MinghaoCheng/Pacman/host/src/Drivers/ldr_matrix.h

/*
 * GNU GENERAL PUBLIC LICENSE
 * Version 1, Mar 2019
 *
 * (C) 2019, Minghao Cheng <chengminghao92@gmail.com>
 */
#ifndef _LDR_MATRIX_
#define _LDR_MATRIX_

#include <stdint.h>

#include "./../BSP/mcp23s17.h"
#include "./../util/Thread.h"
#include "./../util/callback.h"
#include "brd_config.h"

/**
 * Class of Light-Dependent-Resistor matrix
 */
class LDR_matrix: public callback
{
    public:
    LDR_matrix(pthread_t ID, callback *INT_callback);
    virtual ~LDR_matrix(void);
    int8_t init(void);
    
    private:
    pthread_t id;
    MCP23S17 *GPIO;
    virtual void cb_func(uint8_t *param, uint8_t size);
    callback *INT_handler;
};

#endif
